xpix/XATC/fusion360/Baseplate v4.png

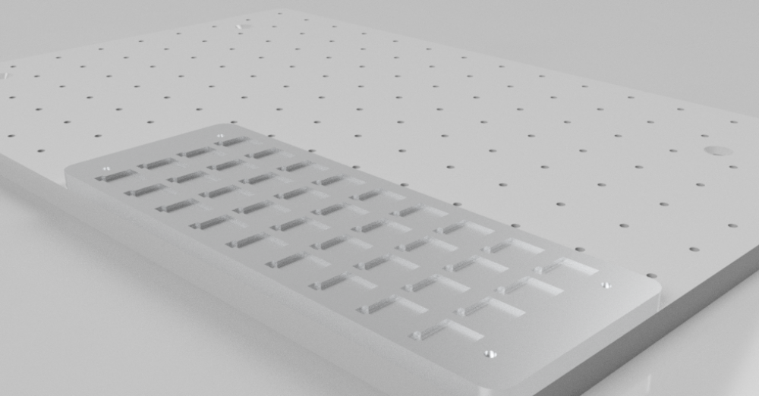
fusion360/Baseplate v4.png
