xpix/XATC/fusion360/ColletNutAdapter v0 v0.png

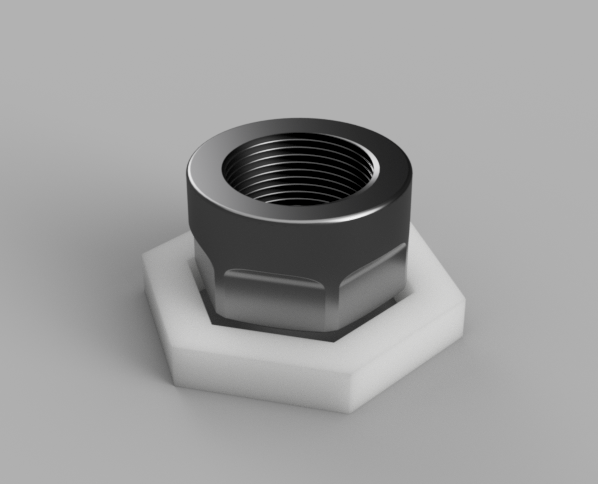
fusion360/ColletNutAdapter v0 v0.png
