xpix/XATC/fusion360/PcbHolder_75x100.png

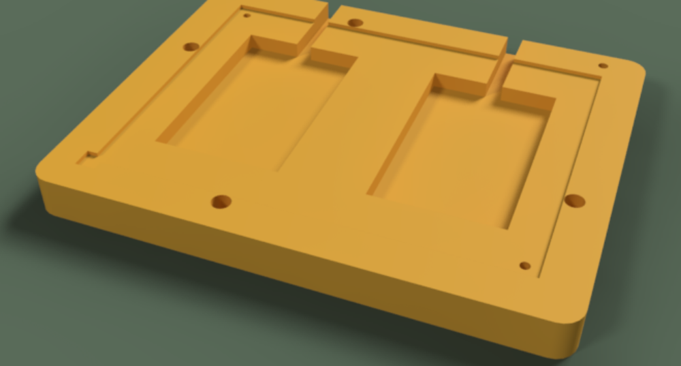
fusion360/PcbHolder_75x100.png
