xpix/XATC/fusion360/XATC Carousel v6.png

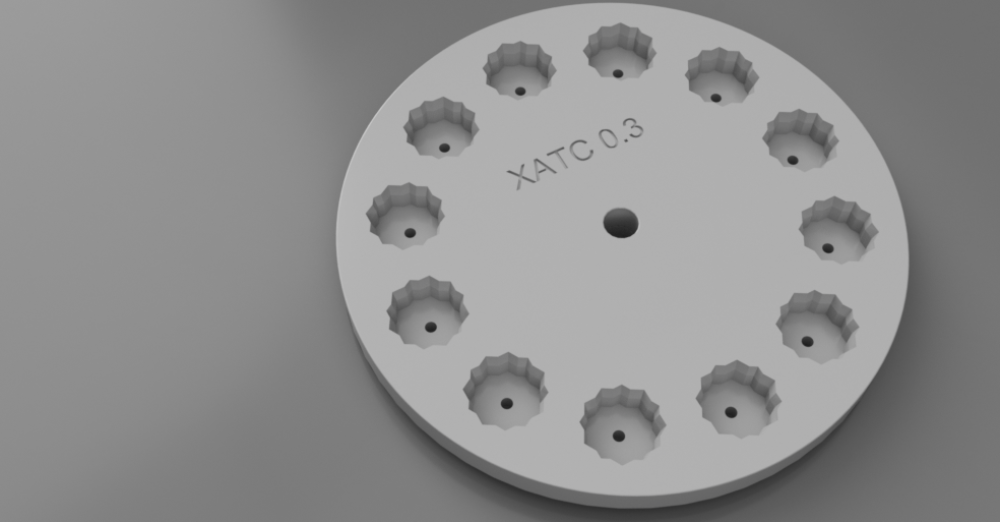
fusion360/XATC Carousel v6.png
