xpix/XATC/fusion360/XATC Endmill Holder v1.png

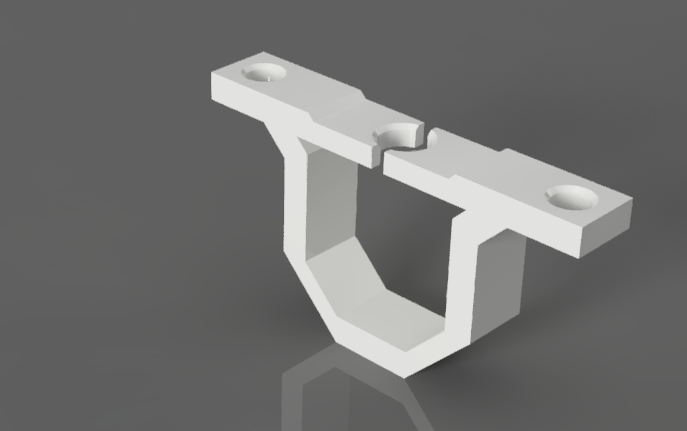
fusion360/XATC Endmill Holder v1.png
