xpix/XATC/fusion360/XTC-Holder v0.png

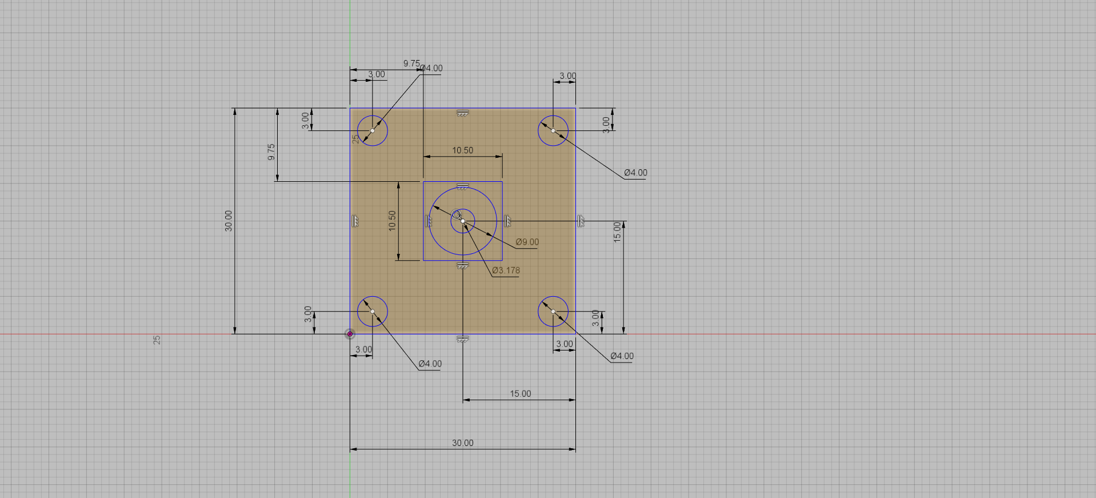
fusion360/XTC-Holder v0.png
