xpix/XATC/fusion360/XTC-Holder.png

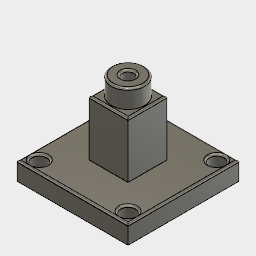
fusion360/XTC-Holder.png
