xpix/XATC/pics/2000px-Degree-Radian_Conversion.svg.png

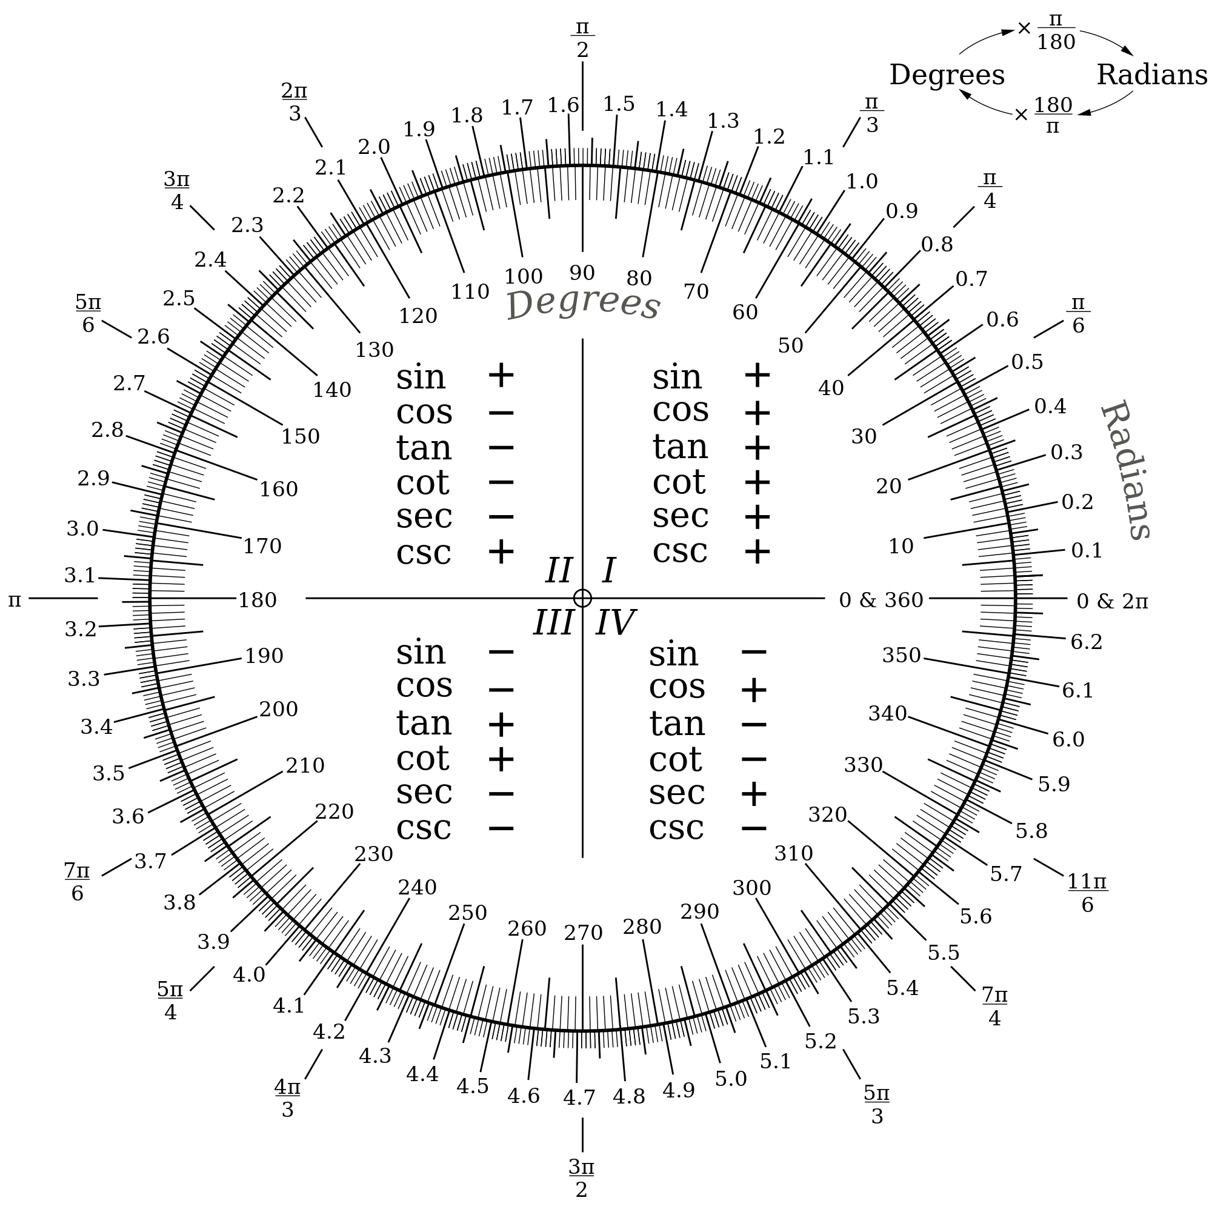
pics/2000px-Degree-Radian_Conversion.svg.png
