xpix/XATC/pics/CarouselV2 v5.png

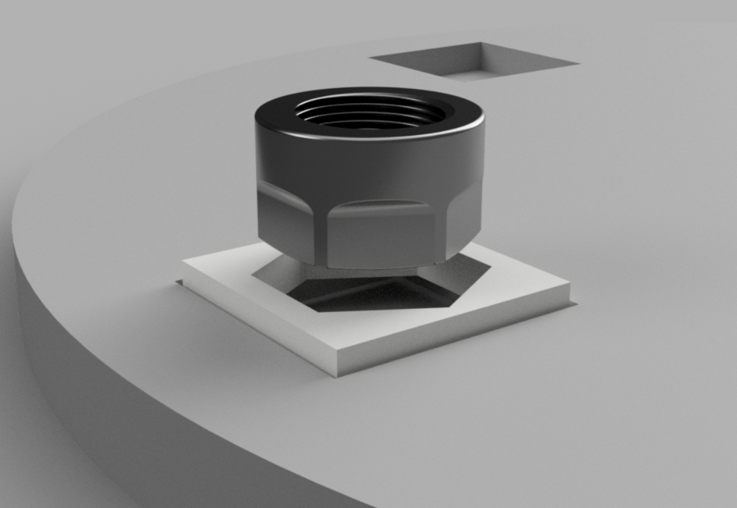
pics/CarouselV2 v5.png
