xpix/XATC/pics/CarouselV2 v8.png

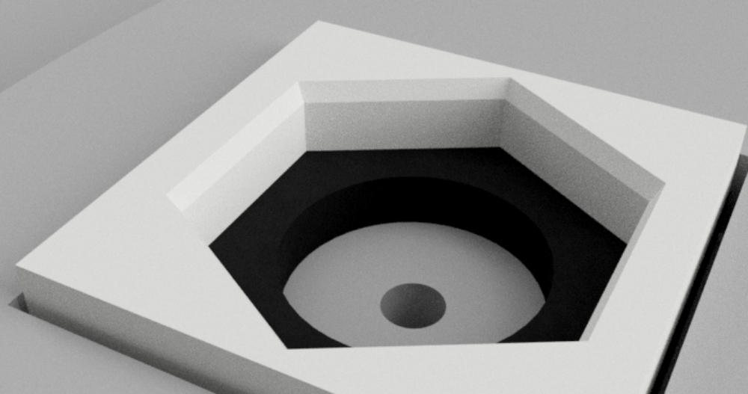
pics/CarouselV2 v8.png
