xpix/XATC/pics/CarouselV2_analysis.PNG

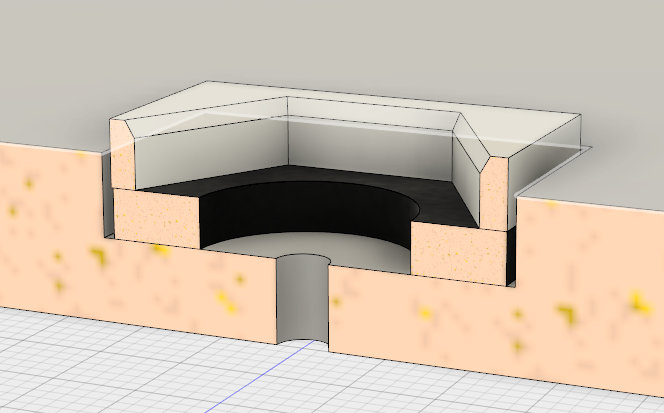
pics/CarouselV2_analysis.PNG
