xpix/XATC/pics/CatchFrame.png

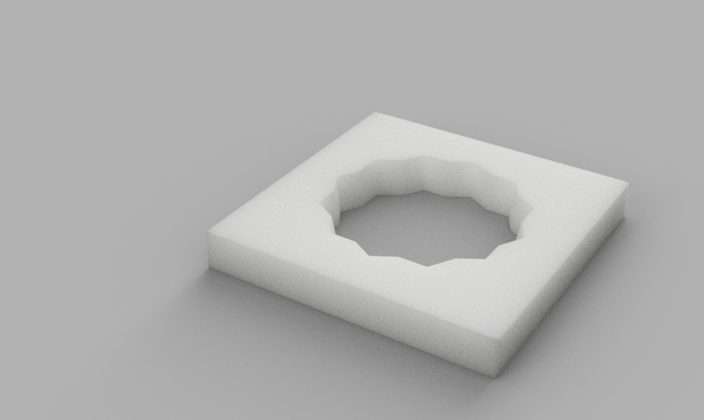
pics/CatchFrame.png
