xpix/XATC/pics/ColletNutAdapter v0 v1.png

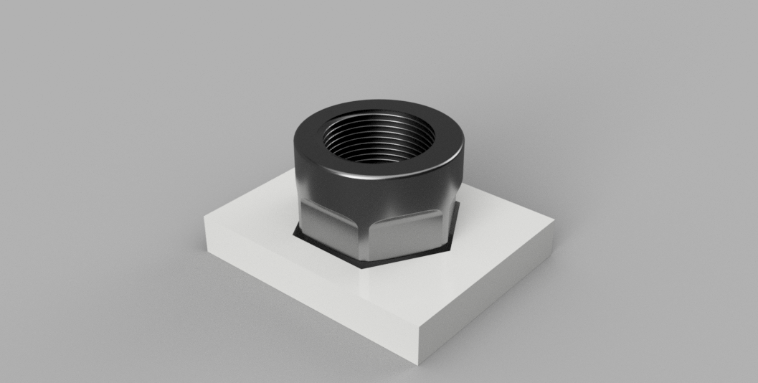
pics/ColletNutAdapter v0 v1.png
