xpix/XATC/pics/ColletNutAdapter v0 v2.png

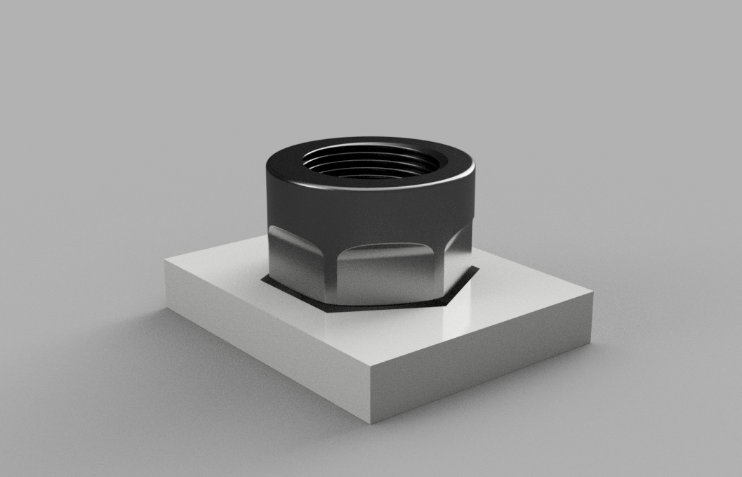
pics/ColletNutAdapter v0 v2.png
