xpix/XATC/pics/ebay_gator_grip.PNG

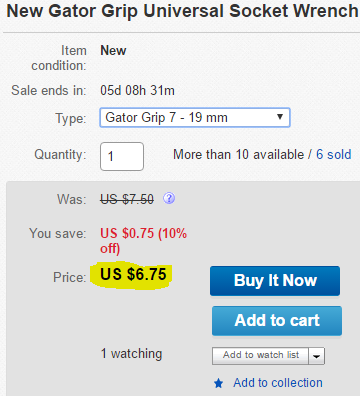
pics/ebay_gator_grip.PNG
