xpix/XATC/pics/EHolder.PNG

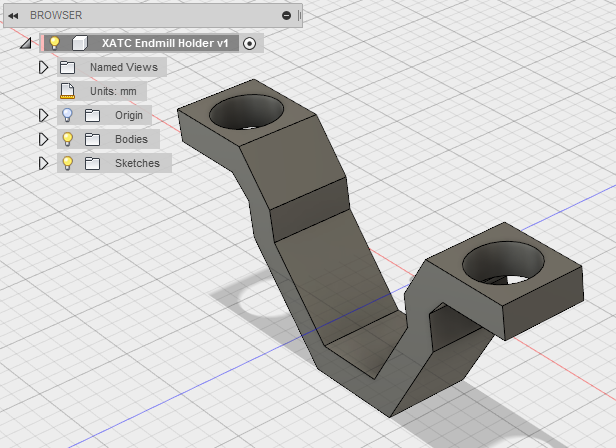
pics/EHolder.PNG
