xpix/XATC/pics/event_explain.png

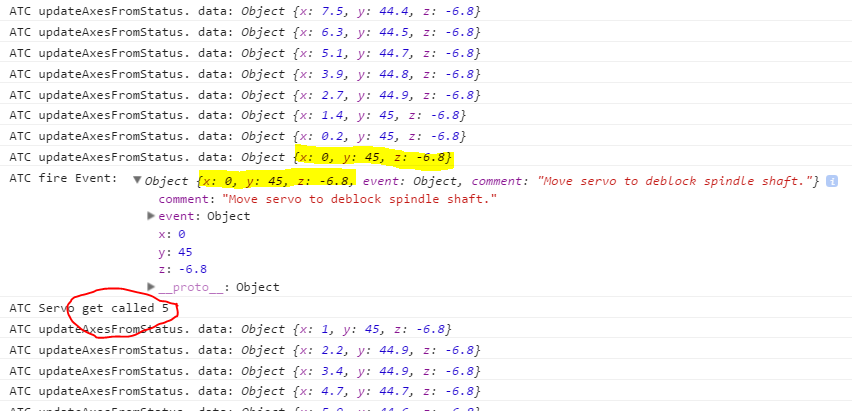
pics/event_explain.png
