xpix/XATC/pics/gplus.PNG

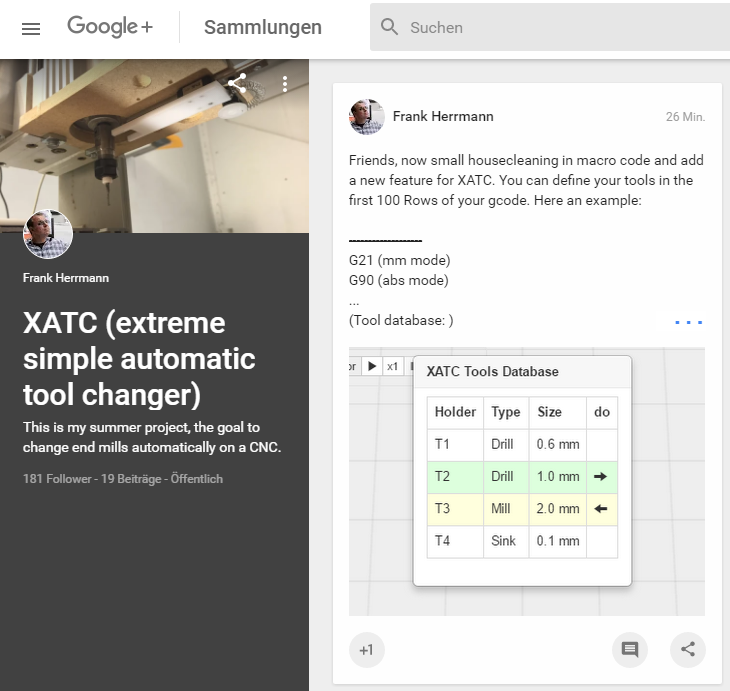
pics/gplus.PNG
