xpix/XATC/pics/IMG_0593.JPG

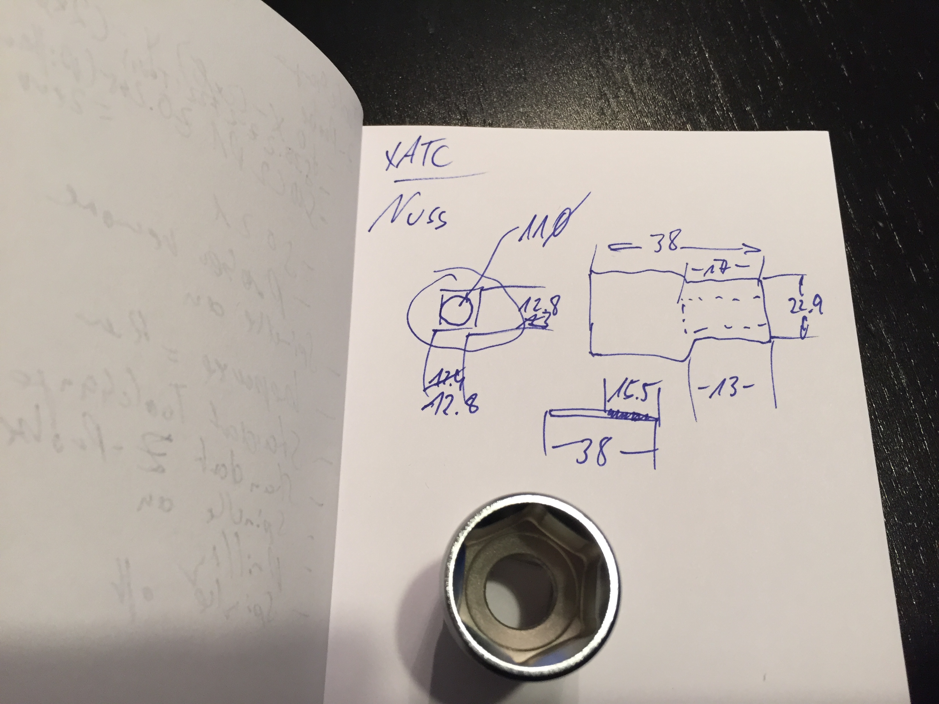
pics/IMG_0593.JPG
