xpix/XATC/pics/tooldatabase_table.PNG

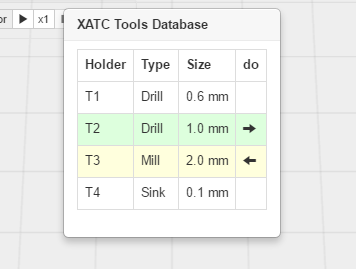
pics/tooldatabase_table.PNG
